GG23800/TravailDuCuir/Sacoche_boules_petanque/Photos/anse.JPG

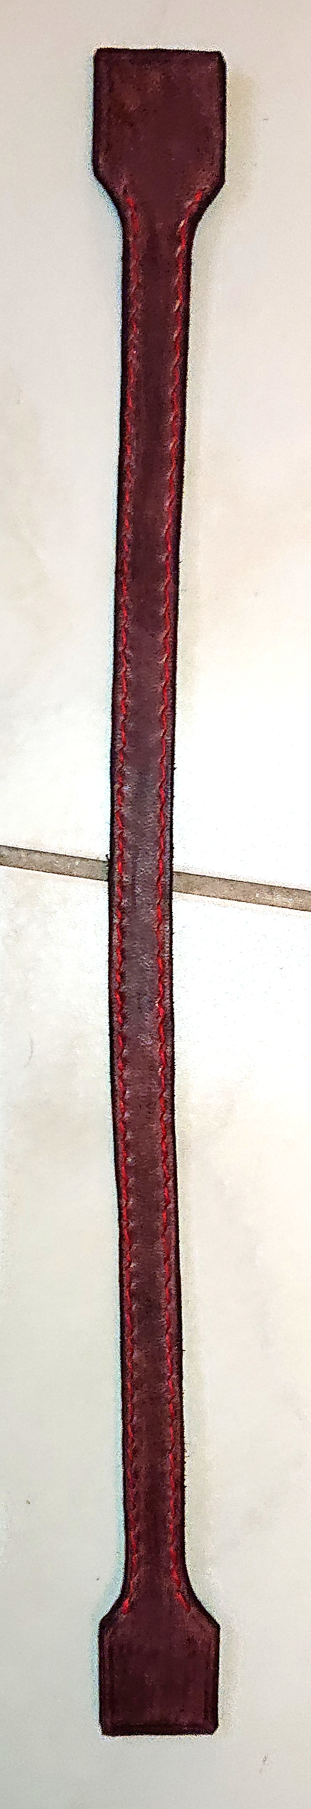
Sacoche_boules_petanque/Photos/anse.JPG
