GG23800/TravailDuCuir/Sacoche_boules_petanque/Photos/cotes_anse.JPG

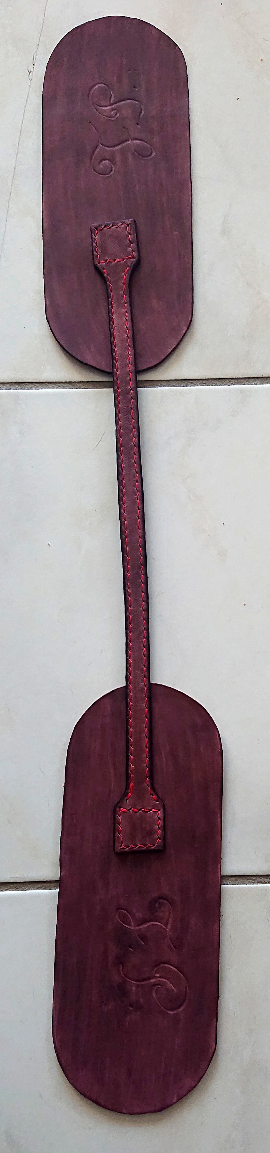
Sacoche_boules_petanque/Photos/cotes_anse.JPG
