GG23800/TravailDuCuir/Sacoche_boules_petanque/Photos/fermeture_arriere.JPG

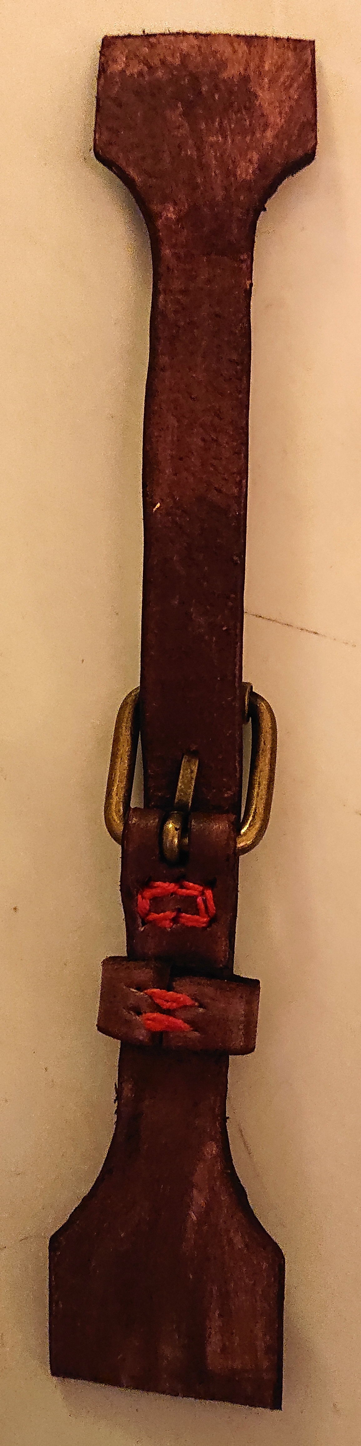
Sacoche_boules_petanque/Photos/fermeture_arriere.JPG
